cassy-de/OWslave/Eagle/Board2.PNG

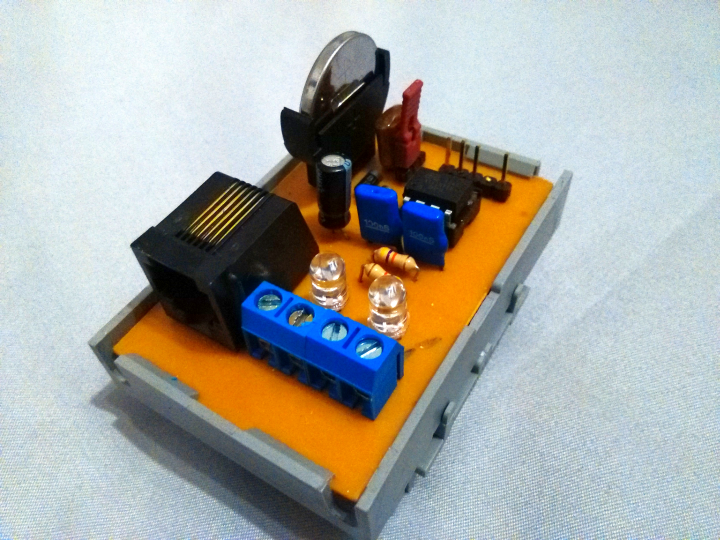
Eagle/Board2.PNG
